AllenNeuralDynamics/harp.device.quac/firmware/inc/quac_app.h

#ifndef QUAC_H
#define QUAC_H
#include <array>
#include <cstdint>
#include <cstring> // for memcpy
#include "pico/util/queue.h"
#include "pico/multicore.h"
#include "config.h"
#include "core1_file_player.h"
#include "harp_core.h"
#include "harp_c_app.h"
#include "harp_message.h"
#include "reg_spec.h"
#include "dma_double_buffer.h"
#include "file_player.h"
#include "sine_wave_player.h"
#include "trapezoid_player.h"
#include "multi_transfer_manager.h"
#include "waveform_settings.h"
#include "pio_ltc264x.h"

using enum reg_type_t;

extern std::array<PIO_LTC264x, NUM_CHANNELS> dacs;
extern queue_t ext_trigger_event_queue;

extern std::array<TimerPacedDMADoubleBuffer<T, READ_BUF_SIZE>, NUM_CHANNELS> bufs;
extern std::array<DMADoubleBuffer<T, READ_BUF_SIZE>*, NUM_CHANNELS> buf_ptrs;
extern std::array<FilePlayer<T, READ_BUF_SIZE>, NUM_CHANNELS> file_players;
extern std::array<SinePlayer<T, READ_BUF_SIZE>, NUM_CHANNELS> sine_players;
extern std::array<TrapezoidPlayer<T, READ_BUF_SIZE>, NUM_CHANNELS> trapezoid_players;
extern MultiTransferManager<T, READ_BUF_SIZE, NUM_CHANNELS> transfer_manager;
extern RegSpec app_reg_specs[];

extern const size_t APP_REG_COUNT;
inline constexpr size_t DAC_START_ADDRESS = HarpCore::APP_REG_START_ADDRESS + 10;
inline constexpr size_t DAC_FINISHED_ADDRESS = HarpCore::APP_REG_START_ADDRESS + 13;

enum player_t: uint8_t
{
    file = 0,
    sine = 1,
    trapezoid = 2
};

struct ext_trigger_event_t
{
    uint32_t channel_start_mask;
    uint64_t timestamp;
};

#pragma pack(push, 1)
struct app_regs_t
{
    // Digital Output
    uint8_t digital_output_port_state;
    uint8_t digital_output_port_set;
    uint8_t digital_output_port_clear;

    // Triggers.
    uint8_t ext_trigger_state;

    float analog_output_port_state[NUM_CHANNELS];
    float& analog_output_channel_0  = analog_output_port_state[0];
    float& analog_output_channel_1  = analog_output_port_state[1];
    float& analog_output_channel_2  = analog_output_port_state[2];
    float& analog_output_channel_3  = analog_output_port_state[3];

    // DAC state masks.
    uint8_t dac_ready;
    uint8_t dac_start;
    uint8_t dac_pause; // 1-bit: pause active channel, 0-bit: unpause paused channel
    uint8_t dac_abort;
    uint8_t dac_finished;

    // External trigger masks per-channel. Assign channel[i] to one or more triggers.
    uint8_t channel_external_triggers[NUM_CHANNELS];

    // Which player is active per channel.
    uint8_t active_players[NUM_CHANNELS];

    // Settings for each distinct player.
    FileSettings file_settings[NUM_CHANNELS];
    FunctionSettings sine_settings[NUM_CHANNELS];
    TrapezoidSettings trapezoid_settings[NUM_CHANNELS];
    //TrapezoidSettings (&sawtooth_settings)[NUM_CHANNELS] = trapezoid_settings;
    //TrapezoidSettings (&triangle_settings)[NUM_CHANNELS] = trapezoid_settings;

};
#pragma pack(pop)

extern app_regs_t app_regs;

void read_digital_output_port_state(uint8_t address);
void write_digital_output_port_state(msg_t& msg);

void write_digital_output_port_set(msg_t& msg);

void write_digital_output_port_clear(msg_t& msg);

void read_ext_trigger_state(uint8_t address);

void read_analog_output_port_state(uint8_t address);
void write_analog_output_port_state(msg_t& msg);

void read_any_analog_output_channel(uint8_t address);
void write_any_analog_output_channel(msg_t& msg);

void read_dac_ready(uint8_t address);

void write_dac_start(msg_t& msg);

void write_dac_pause(msg_t& msg);

void write_dac_abort(msg_t& msg);

void write_any_channel_external_triggers(msg_t& msg);

void write_any_channel_active_player(msg_t& msg);

void select_player(size_t channel, player_t player);

/**
 * \brief handler function to write any settings to a specific player type.
 * \details templated function such that it can be specialized to a specific
 *  player type.
 */
template <typename SETTINGS, SETTINGS* settings_arr, player_t PLAYER_ENUM>
void write_settings(msg_t& msg)
{
    // Convert address to output channel with pointer arithmetic.
    const RegSpec& spec = HarpCore::reg_address_to_spec(msg.header.address);
    size_t i = ((SETTINGS*)spec.base_ptr - settings_arr);
    // Error if we try to change the specified channel while it's busy.
    if (bufs[i].is_transferring())
    {
        if (!HarpCore::is_muted())
            HarpCore::send_harp_reply(WRITE_ERROR, msg.header.address);
        return;
    }
    HarpCore::copy_msg_payload_to_register(msg);
    // Re-setup the player if it is active. (i.e: apply_settings() and setup())
    if (player_t(app_regs.active_players[i]) == PLAYER_ENUM)
        select_player(i, PLAYER_ENUM);
    if (!HarpCore::is_muted())
        HarpCore::send_harp_reply(WRITE, msg.header.address);
}

// These are generated from the above function template
void write_any_file_settings(msg_t& msg);
void write_any_sine_settings(msg_t& msg);
void write_any_trapezoid_settings(msg_t& msg);

void read_any_waveform_hash(uint8_t address);

void write_any_waveform_data(msg_t& msg);

void reset_app();


bool player_is_ready(size_t channel, player_t player_type);

void update_app();


/// Callbacks
void handle_external_trigger();



#endif // QUAC_H
