AllenNeuralDynamics/harp.device.quac/firmware/tests/read_sd_card/src/main.cpp

/* main.c
Copyright 2021 Carl John Kugler III

Licensed under the Apache License, Version 2.0 (the License); you may not use
this file except in compliance with the License. You may obtain a copy of the
License at

   http://www.apache.org/licenses/LICENSE-2.0
Unless required by applicable law or agreed to in writing, software distributed
under the License is distributed on an AS IS BASIS, WITHOUT WARRANTIES OR
CONDITIONS OF ANY KIND, either express or implied. See the License for the
specific language governing permissions and limitations under the License.
*/

#include <stdio.h>
//
#include "pico/stdlib.h"
//
#include "f_util.h"
#include "ff.h"
#include "hw_config.h"

/*

This file should be tailored to match the hardware design.

See
https://github.com/carlk3/no-OS-FatFS-SD-SDIO-SPI-RPi-Pico/tree/main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

*/

#include "hw_config.h"

/* SDIO Interface */
static sd_sdio_if_t sdio_if = {
    /*
    Pins CLK_gpio, D1_gpio, D2_gpio, and D3_gpio are at offsets from pin D0_gpio.
    The offsets are determined by sd_driver\SDIO\rp2040_sdio.pio.
        CLK_gpio = (D0_gpio + SDIO_CLK_PIN_D0_OFFSET) % 32;
        As of this writing, SDIO_CLK_PIN_D0_OFFSET is 30,
            which is -2 in mod32 arithmetic, so:
    */

//   CLK_gpio = D0_gpio - 2; -> derived from D0_gpio.
    .CMD_gpio = 22,  // DO_gpio - 1 -> derived from D0_gpio.
    .D0_gpio = 23,
//    D1_gpio = D0_gpio + 1; -> derived from D0_gpio.
//    D2_gpio = D0_gpio + 2; -> derived from D0_gpio.
//    D3_gpio = D0_gpio + 3; -> derived from D0_gpio.
    .baud_rate = 150 * 1000 * 1000 / 6  // RP2350: */6 -> 25 MHz
};

/* Hardware Configuration of the SD Card socket "object" */
static sd_card_t sd_card = {.type = SD_IF_SDIO, .sdio_if_p = &sdio_if};

/**
 * @brief Get the number of SD cards.
 *
 * @return The number of SD cards, which is 1 in this case.
 */
size_t sd_get_num() { return 1; }

/**
 * @brief Get a pointer to an SD card object by its number.
 *
 * @param[in] num The number of the SD card to get.
 *
 * @return A pointer to the SD card object, or @c NULL if the number is invalid.
 */
sd_card_t* sd_get_by_num(size_t num) {
    if (0 == num) {
        // The number 0 is a valid SD card number.
        // Return a pointer to the sd_card object.
        return &sd_card;
    } else {
        // The number is invalid. Return @c NULL.
        return NULL;
    }
}

/**
 * @brief The main function of the program.
 *
 * @details This function initializes the stdio interface, prints a greeting to the
 * console, mounts the SD card, writes a message to a file, and unmounts the SD card.
 *
 */
int main() {
    stdio_init_all();
    while (!stdio_usb_connected()){ sleep_ms(100);} // Wait for user to open com port.
    printf("Hello, world, from a Raspberry Pi Pico!\r\n");

    // See FatFs - Generic FAT Filesystem Module, "Application Interface",
    // http://elm-chan.org/fsw/ff/00index_e.html
    FATFS fs;
    FRESULT fr = f_mount(&fs, "", 1);
    if (FR_OK != fr) {
        panic("f_mount error: %s (%d)\n", FRESULT_str(fr), fr);
        return -1;
    }

    FIL fil;
    char buffer[100]; /* File read buffer */
    UINT bytes_read;        /* Bytes read */
    const char* const filename = "channel_0.bin";

    // Open a file
    fr = f_open(&fil, filename, FA_READ);
    if (fr != FR_OK) {
        printf("Could not open: %s", filename);
        return -1;
    }
    // Read data from the file
    fr = f_read(&fil, buffer, sizeof(buffer) - 1, &bytes_read);
    if (fr != FR_OK) {
        printf("Could not read from file.");
        return -1;
    }
    buffer[bytes_read] = '\0'; // Null-terminate the string
    // Process the read data (e.g., print it)
    printf("Read: %s\r\n", buffer);
    // Close the file
    fr = f_close(&fil);
    if (FR_OK != fr) {
        printf("f_close error: %s (%d)\n", FRESULT_str(fr), fr);
    }

    f_unmount("");
    printf("Goodbye, world!\r\n");
    for (;;);
}
