AllenNeuralDynamics/harp.device.quac/firmware/tests/abort/src/main.cpp

#include <stdio.h>
#include <pico/stdlib.h>
#include <dma_double_buffer.h>
#include <hardware/dma.h>
#include <hardware/pio.h>
#include <pio_ltc264x.h>
#include "f_util.h"
#include "ff.h"
#include "hw_config.h"

inline constexpr uint32_t WORD_COUNT = 32768;

using T = uint16_t;

#define PICO_PIN (4)
#define SCK_PIN (5)
#define CS_PIN (6)

int main() {
    UINT bytes_read;

    stdio_init_all();
    while (!stdio_usb_connected()){ sleep_ms(100);} // Wait for user to open com port.
    printf("Hello, world, from a Raspberry Pi Pico!\r\n");

    // Setup PIO Block for DAC communication.
    PIO_LTC264x dac(pio2, SCK_PIN, PICO_PIN);
    dac.start();

    // Setup transfer rate for 500K words-per-sec. Assume soure clock of 150MHz.
    int dma_timer_chan = dma_claim_unused_timer(true);
    printf("Claimed DMA Timer %d.\r\n", dma_timer_chan);
    dma_timer_set_fraction(dma_timer_chan, 1, 30000); // 5 KHz
    dreq_num_t pacing_signal = dreq_num_t(dma_get_timer_dreq(dma_timer_chan));

    // Create double-buffer. Note: buffer is sized in T-size, not byte size.
    DMADoubleBuffer<T, WORD_COUNT> buf(pacing_signal, &pio2->txf[dac.get_sm()]);

    // Sanity check.
    if (buf.is_aborted())
        printf("ERROR: Buffer detected as aborted before even transferring.\r\n");

    // Copy of the current idle buffer name so we can track when it toggles.
    printf("Starting transfer.\r\n");
    buf.setup_last_dma_transfer(WORD_COUNT); // only do one buffer transfer.
    buf.start_transfer();
    // Wait for transfer to start. (Should be instant.)
    printf("Waiting for transfer to start.\r\n");
    while (!buf.is_transferring()){}
    sleep_ms(1);
    printf("Aborting transfer.\r\n");
    buf.abort_transfer();
    if (!buf.is_transferring())
        printf("No longer transferring.\r\n");
    else
        printf("ERROR: Transfer is still transferring or detected as such.\r\n");
    if (buf.is_aborted())
        printf("Transfer detected as aborted.\r\n");
    else
        printf("ERROR: Transfer not aborted or not detected as such.\r\n");
    printf("Resetting dma configuration.\r\n");
    buf.reset_transfer_config();
    if (buf.is_aborted())
        printf("ERROR: Buffer still detected as aborted.\r\n");
    else
        printf("Buffer no longer detected as aborted.\r\n");

    printf("Goodbye, world.\r\n");
    for (;;);
}
