AllenNeuralDynamics/harp.device.quac/firmware/tests/sine_player/src/main.cpp

#include "pico/stdlib.h"
#include "hardware/dma.h"
#include "hardware/pio.h"
#include "pio_ltc264x.h"
#include "dma_double_buffer.h"
#include "waveform_settings.h"
#include "sine_wave_player.h"
#include <cstdint>
#include <cstdio>

using T = uint16_t;
inline constexpr size_t CHUNK_SIZE = 32768; // must be factor of 2.
inline constexpr size_t BUF_SIZE = CHUNK_SIZE / sizeof(T);

struct DACPins
{
    uint32_t pico;
    uint32_t sck;
    uint32_t cs;
};

DACPins dac_pins{.pico = 4, .sck = 5, .cs = 6};

int main() {
    stdio_init_all();
    while (!stdio_usb_connected()){ sleep_ms(100);} // Wait for user to open com port.
    printf("Hello, world, from a Raspberry Pi Pico!\r\n");
    // Setup PIO Block for DAC communication.
    PIO_LTC264x dac(pio2, dac_pins.sck, dac_pins.pico);
    dac.start();
    PIO& pio = dac.get_pio(); // TODO: dac.get_tx_fifo()
    int32_t sm = dac.get_sm();
    TimerPacedDMADoubleBuffer<T, BUF_SIZE> buf(&pio->txf[sm]);
    printf("Buf is_aborted? %s\r\n", buf.is_aborted()? "true": "false");
    // Create SinePlayer
    SinePlayer<T, BUF_SIZE> player;
    FunctionSettings settings;
    settings.amplitude_volts = 5; // amplitude from center, not peak-to-peak.
    settings.vertical_shift_volts = 2.5;
//    printf("settings:\r\n");
//    printf("update_frequency_hz: %u\r\n", settings.update_frequency_hz);
//    printf("amplitude: %f\r\n", settings.amplitude_volts);
//    printf("duration_us: %u\r\n", settings.duration_us);
//    printf("frequency_hz: %u\r\n", settings.frequency_hz);
//    printf("period_us: %u\r\n", settings.period_us());
//    printf("vshift: %f\r\n", settings.vertical_shift_volts);
    player.claim_buffer(&buf);
    printf("applying settings.\r\n");
    player.apply_settings(settings);
    printf("Is SinePlayer is ready? %s\r\n", player.is_ready()? "true": "false");
    player.setup(); // should arm.
    printf("Is SinePlayer is ready? %s\r\n", player.is_ready()? "true": "false");
    sleep_ms(500);
    printf("Starting.\r\n");
    buf.start_transfer();
    while(player.is_busy())
        player.update();
    printf("Done playing!\r\n");
    printf("Is SinePlayer is ready? %s\r\n", player.is_ready()? "true": "false");
    player.cleanup(); // Release buffer.
    // Unmount the file system.
    printf("All transfers complete! Goodbye, world!\r\n");
    for (;;);
}
